pdaxrom/N64cart/pics/IMG_20220826_213916.jpg

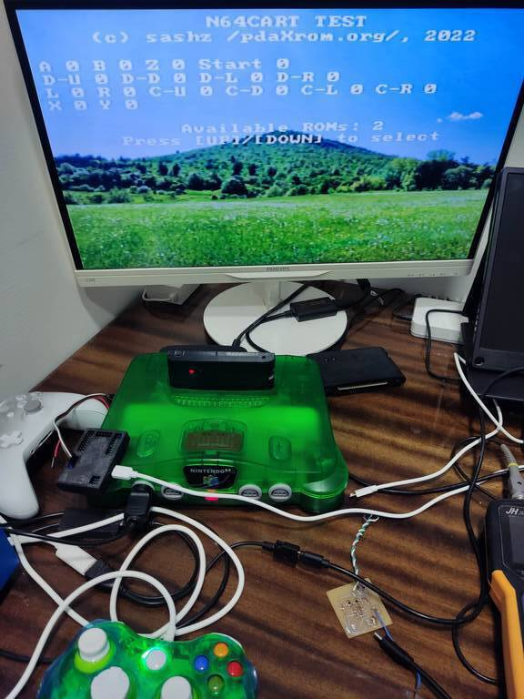
pics/IMG_20220826_213916.jpg
