pdaxrom/N64cart/rom/assets/UbuntuMono-Regular-8.png

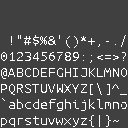
rom/assets/UbuntuMono-Regular-8.png
