pdaxrom/N64cart/fw/n64.h

/**
 * Copyright (c) 2022 Konrad Beckmann
 *
 * Copyright (c) 2022-2026 sashz /pdaXrom.org/
 *
 * SPDX-License-Identifier: BSD-3-Clause
 */

#pragma once

#define N64_AD0  0
#define N64_AD1  1
#define N64_AD2  2
#define N64_AD3  3
#define N64_AD4  4
#define N64_AD5  5
#define N64_AD6  6
#define N64_AD7  7
#define N64_AD8  8
#define N64_AD9  9
#define N64_AD10 10
#define N64_AD11 11
#define N64_AD12 12
#define N64_AD13 13
#define N64_AD14 14
#define N64_AD15 15
#define N64_ALEL 16
#define N64_ALEH 17
#define N64_WRITE 18
#define N64_READ 19
#define N64_CIC_DCLK    (20)
#define N64_CIC_DIO     (21)
#define N64_COLD_RESET  (22)

#ifdef N64CART_RP2040_PICO_LITE

#define N64_SI_DATA (25)
#define N64_SI_CLK (26)
#define N64_NMI (27)
#define N64_INT (28)

#else

#define N64_SI_DATA (23)
#define N64_SI_CLK (24)
#define N64_NMI (26)
#define N64_INT (27)

#endif
