pdaxrom/N64cart/fw/romfs/newlib-romfs.h

#ifndef __NEWLIB_ROMFS_H__
#define __NEWLIB_ROMFS_H__

#include <sys/types.h>

#ifdef __cplusplus
extern "C" {
#endif

int newlib_romfs_init(void);

#ifdef __cplusplus
}
#endif

#endif /* __NEWLIB_ROMFS_H__ */
