pdaxrom/N64cart/fw/romfs/test.c

/**
 * Copyright (c) 2022-2023 sashz /pdaXrom.org/
 *
 * SPDX-License-Identifier: BSD-3-Clause
 */

#include <stdio.h>
#include <stdlib.h>
#include <string.h>
#include <stdbool.h>
#include <errno.h>
#include <inttypes.h>
#include "romfs.h"
#include "test_flash.h"

#if defined(__linux__) || defined(__APPLE__)
#define ANSI_COLOR_RED     "\x1b[31m"
#define ANSI_COLOR_GREEN   "\x1b[32m"
#define ANSI_COLOR_YELLOW  "\x1b[33m"
#define ANSI_COLOR_CYAN    "\x1b[36m"
#define ANSI_COLOR_MAGENTA "\x1b[35m"
#define ANSI_COLOR_RESET   "\x1b[0m"
#else
#define ANSI_COLOR_RED     ""
#define ANSI_COLOR_GREEN   ""
#define ANSI_COLOR_YELLOW  ""
#define ANSI_COLOR_CYAN    ""
#define ANSI_COLOR_MAGENTA ""
#define ANSI_COLOR_RESET   ""
#endif

static uint8_t *flash_base = NULL;

const int NORMAL_CHUNK_SIZE = 256;
const int NORMAL_CHUNKS_PER_FILE = 20; // Creates 5KB files (256 * 20)
const int SMALL_FILE_SIZE = 1; // For testing file list limits

typedef struct {
    char name[ROMFS_MAX_NAME_LEN];
    uint32_t size;
    int file_index;
} random_fill_entry;

static uint32_t rng_state;
static uint64_t rng_calls;

/* Explicit 32-bit arithmetic gives the same sequence on every host libc. */
static uint32_t test_random(void)
{
    rng_state = rng_state * 1664525u + 1013904223u;
    rng_calls++;
    return rng_state;
}

static void free_file_list(char **files, int count)
{
    for (int i = 0; i < count; i++) {
        free(files[i]);
    }
    free(files);
}

static bool flash_ok(void)
{
    const test_flash_stats *stats = test_flash_get_stats();
    return stats->rejected == 0 && stats->injected == 0;
}

static bool close_test_file(romfs_file *file)
{
    uint32_t err = romfs_close_file(file);
    if (err != ROMFS_NOERR) {
        fprintf(stderr, "Failed to close %s: %s\n", file->entry.name, romfs_strerror(err));
        return false;
    }
    return true;
}

// Fills a buffer with deterministic dummy data based on an index
static void create_test_data(uint8_t *buffer, size_t size, int file_idx, int chunk_idx)
{
    for (size_t i = 0; i < size; i++) {
        buffer[i] = (uint8_t)((file_idx + chunk_idx + i) & 0xFF);
    }
}

static bool test_service_sector_protection(uint16_t *flash_map, uint32_t map_size)
{
    printf(ANSI_COLOR_YELLOW "\n--- Running Service Sector Protection Test ---\n" ANSI_COLOR_RESET);

    if (!romfs_format()) {
        fprintf(stderr, ANSI_COLOR_RED "Failed to format filesystem for service sector test\n" ANSI_COLOR_RESET);
        return false;
    }

    romfs_entry firmware = {0};
    romfs_entry flashmap = {0};
    if (romfs_get_entry("firmware", &firmware) != ROMFS_NOERR ||
            romfs_get_entry("flashmap", &flashmap) != ROMFS_NOERR) {
        fprintf(stderr, ANSI_COLOR_RED "Cannot read service entries\n" ANSI_COLOR_RESET);
        return false;
    }

    uint32_t first_data_sector = flashmap.start +
                                 (flashmap.size + ROMFS_FLASH_SECTOR - 1) / ROMFS_FLASH_SECTOR;
    uint32_t total_sectors = map_size / sizeof(uint16_t);
    if (first_data_sector >= total_sectors || firmware.size > first_data_sector * ROMFS_FLASH_SECTOR) {
        fprintf(stderr, ANSI_COLOR_RED "Invalid service sector layout\n" ANSI_COLOR_RESET);
        return false;
    }

    for (uint32_t i = 0; i < firmware.size; i++) {
        flash_base[i] = (uint8_t) ((i * 31u + 0x5au) & 0xffu);
    }

    // Simulate an old or damaged flash map that marks firmware and metadata
    // sectors as free. A user file must never be allocated in this range.
    for (uint32_t i = 0; i < first_data_sector; i++) {
        flash_map[i] = 0xffff;
    }

    uint8_t *io_buffer = malloc(ROMFS_FLASH_SECTOR);
    uint8_t *payload = malloc(ROMFS_FLASH_SECTOR);
    if (!io_buffer || !payload) {
        fprintf(stderr, ANSI_COLOR_RED "Allocation failure in service sector test\n" ANSI_COLOR_RESET);
        free(io_buffer);
        free(payload);
        return false;
    }
    memset(payload, 0xa5, ROMFS_FLASH_SECTOR);

    bool success = true;
    romfs_file file = {0};
    if (romfs_create_file("service-guard.bin", &file, ROMFS_MODE_READWRITE, ROMFS_TYPE_MISC,
                          io_buffer) != ROMFS_NOERR ||
            romfs_write_file(payload, ROMFS_FLASH_SECTOR, &file) != ROMFS_FLASH_SECTOR ||
            romfs_close_file(&file) != ROMFS_NOERR) {
        fprintf(stderr, ANSI_COLOR_RED "Failed to write service sector test file: %s\n" ANSI_COLOR_RESET,
                romfs_strerror(file.err));
        success = false;
        goto cleanup;
    }

    if (file.entry.start < first_data_sector) {
        fprintf(stderr, ANSI_COLOR_RED "User file allocated protected sector %u (< %u)\n" ANSI_COLOR_RESET,
                file.entry.start, first_data_sector);
        success = false;
        goto cleanup;
    }

    for (uint32_t i = 0; i < firmware.size; i++) {
        uint8_t expected = (uint8_t) ((i * 31u + 0x5au) & 0xffu);
        if (flash_base[i] != expected) {
            fprintf(stderr, ANSI_COLOR_RED "Firmware changed at offset 0x%08x\n" ANSI_COLOR_RESET, i);
            success = false;
            goto cleanup;
        }
    }

    romfs_file protected_file = {0};
    if (romfs_open_append("firmware", &protected_file, ROMFS_TYPE_MISC, io_buffer) != ROMFS_ERR_OPERATION ||
            romfs_delete("firmware") != ROMFS_ERR_OPERATION ||
            romfs_rename("firmware", "firmware.old") != ROMFS_ERR_OPERATION ||
            romfs_create_file("fake-service", &protected_file, ROMFS_MODE_READWRITE, ROMFS_TYPE_FIRMWARE,
                              io_buffer) != ROMFS_ERR_OPERATION) {
        fprintf(stderr, ANSI_COLOR_RED "Service entry mutation was not rejected\n" ANSI_COLOR_RESET);
        success = false;
    }

cleanup:
    romfs_delete("service-guard.bin");
    free(io_buffer);
    free(payload);
    success = romfs_format() && success;
    return success;
}

// Shuffles an array of strings
static void shuffle_filenames(char **array, size_t n)
{
    if (n > 1) {
        for (size_t i = 0; i < n - 1; i++) {
            size_t j = i + test_random() % (n - i);
            char *t = array[j];
            array[j] = array[i];
            array[i] = t;
        }
    }
}

// Gets a list of all user-created files
static int get_file_list(char ***file_list_out)
{
    *file_list_out = NULL;
    int count = 0;
    int capacity = 128;
    char **files = malloc(capacity * sizeof(*files));
    if (!files) {
        fprintf(stderr, "Failed to allocate file list\n");
        return -1;
    }

    romfs_file file = {0};
    uint32_t err = romfs_list(&file, true);
    while (err == ROMFS_NOERR) {
        if (file.entry.attr.names.type == ROMFS_TYPE_MISC) {
            if (count == capacity) {
                int new_capacity = capacity * 2;
                char **new_files = realloc(files, new_capacity * sizeof(*files));
                if (!new_files) {
                    fprintf(stderr, "Failed to expand file list\n");
                    free_file_list(files, count);
                    return -1;
                }
                files = new_files;
                capacity = new_capacity;
            }
            files[count] = strdup(file.entry.name);
            if (!files[count]) {
                fprintf(stderr, "Failed to copy filename\n");
                free_file_list(files, count);
                return -1;
            }
            count++;
        }
        err = romfs_list(&file, false);
    }
    if (err != ROMFS_ERR_NO_FREE_ENTRIES) {
        fprintf(stderr, "Failed to list files: %s\n", romfs_strerror(err));
        free_file_list(files, count);
        return -1;
    }
    *file_list_out = files;
    return count;
}

// Returns the number of complete files, or -1 on an unexpected failure.
// NO_SPACE / NO_FREE_ENTRIES are expected only in these capacity scenarios.
static int fill_drive(const char *prefix, int max_chunks_per_file, int chunk_size, bool random_size)
{
    int file_idx = 0;
    int result = -1;
    uint8_t *test_data = malloc(chunk_size);
    uint8_t *io_buffer = malloc(ROMFS_FLASH_SECTOR);
    if (!test_data || !io_buffer) {
        fprintf(stderr, "Failed to allocate fill buffers\n");
        goto cleanup;
    }

    while (true) {
        char filename[ROMFS_MAX_NAME_LEN];
        snprintf(filename, sizeof(filename), "%s%04d.dat", prefix, file_idx);
        romfs_file file = {0};
        uint32_t err = romfs_create_file(filename, &file, ROMFS_MODE_READWRITE, ROMFS_TYPE_MISC, io_buffer);
        if (err != ROMFS_NOERR) {
            if (err == ROMFS_ERR_NO_FREE_ENTRIES || err == ROMFS_ERR_NO_SPACE) {
                printf("\nCapacity reached after %d files: %s\n", file_idx, romfs_strerror(err));
                result = file_idx;
            } else {
                fprintf(stderr, "Failed to create %s: %s\n", filename, romfs_strerror(err));
            }
            break;
        }

        printf(ANSI_COLOR_MAGENTA "Creating %s... \r" ANSI_COLOR_RESET, filename);
        fflush(stdout);
        int chunks = random_size ? 1 + test_random() % max_chunks_per_file : max_chunks_per_file;
        bool no_space = false;
        bool write_ok = true;
        for (int j = 0; j < chunks; j++) {
            create_test_data(test_data, chunk_size, file_idx, j);
            uint32_t written = romfs_write_file(test_data, chunk_size, &file);
            if (written != (uint32_t)chunk_size || file.err != ROMFS_NOERR) {
                no_space = file.err == ROMFS_ERR_NO_SPACE && written < (uint32_t)chunk_size;
                write_ok = false;
                if (!no_space) {
                    fprintf(stderr, "Write failed for %s: %u/%d bytes, %s\n",
                            filename, written, chunk_size, romfs_strerror(file.err));
                }
                break;
            }
        }
        uint32_t close_err = romfs_close_file(&file);
        if (close_err != ROMFS_NOERR) {
            fprintf(stderr, "Close failed for %s: %s\n", filename, romfs_strerror(close_err));
            break;
        }
        if (!write_ok) {
            if (!no_space) {
                break;
            }
            /* This set verifies complete files; test_io checks partial data. */
            err = romfs_delete(filename);
            if (err != ROMFS_NOERR) {
                fprintf(stderr, "Failed to discard %s: %s\n", filename, romfs_strerror(err));
                break;
            }
            printf("\nData space exhausted after %d complete files.\n", file_idx);
            result = file_idx;
            break;
        }
        file_idx++;
    }

cleanup:
    free(io_buffer);
    free(test_data);
    return result;
}

// Verifies the contents of all user files on the drive, works with random sizes.
static bool verify_drive(uint32_t chunk_size)
{
    printf(ANSI_COLOR_CYAN "\nVerifying all files...\n" ANSI_COLOR_RESET);
    bool success = true;
    char** file_list = NULL;
    int file_count = get_file_list(&file_list);
    if (file_count <= 0) {
        if (file_list) {
            free(file_list);
        }
        if (file_count == 0) {
            printf("No files to verify.\n");
            return true;
        }
        return false;
    }

    uint8_t* read_buffer = malloc(chunk_size);
    uint8_t* expected_data = malloc(chunk_size);
    if (!read_buffer || !expected_data) {
        free(read_buffer);
        free(expected_data);
        free_file_list(file_list, file_count);
        fprintf(stderr, "Failed to allocate verification buffers\n");
        return false;
    }

    for (int i = 0; i < file_count; i++) {
        printf(ANSI_COLOR_MAGENTA "Verifying %s... \r" ANSI_COLOR_RESET, file_list[i]);
        fflush(stdout);

        int file_idx = -1;
        if (sscanf(file_list[i], "file%d.dat", &file_idx) != 1) {
            if (sscanf(file_list[i], "rfile%d.dat", &file_idx) != 1) {
                if (sscanf(file_list[i], "ifile%d.dat", &file_idx) != 1) {
                    if (sscanf(file_list[i], "rndfile%d.dat", &file_idx) != 1) {
                        sscanf(file_list[i], "sfile%d.dat", &file_idx);
                    }
                }
            }
        }

        if (file_idx < 0) {
            fprintf(stderr, "Unexpected verification filename: %s\n", file_list[i]);
            success = false;
            continue;
        }
        romfs_file file = {0};
        uint8_t *romfs_io_buffer = malloc(ROMFS_FLASH_SECTOR);
        if (!romfs_io_buffer) {
            fprintf(stderr, "Failed to allocate verification IO buffer\n");
            success = false;
            break;
        }
        if (romfs_open_file(file_list[i], &file, romfs_io_buffer) != ROMFS_NOERR) {
            fprintf(stderr, ANSI_COLOR_RED "\nFailed to open file for verification: %s\n" ANSI_COLOR_RESET, file_list[i]);
            success = false;
            free(romfs_io_buffer);
            continue;
        }

        bool file_ok = true;
        uint32_t total_bytes_read = 0;
        int chunk_idx = 0;
        while(total_bytes_read < file.entry.size) {
            uint32_t remaining_bytes = file.entry.size - total_bytes_read;
            uint32_t bytes_to_read = remaining_bytes > chunk_size ? chunk_size : remaining_bytes;

            uint32_t bytes_read = romfs_read_file(read_buffer, bytes_to_read, &file);
            if (bytes_read != bytes_to_read ||
                    (file.err != ROMFS_NOERR && file.err != ROMFS_ERR_EOF)) {
                fprintf(stderr, ANSI_COLOR_RED "\nRead error on %s, chunk %d. Expected %d, got %d\n" ANSI_COLOR_RESET, file_list[i],
                        chunk_idx, bytes_to_read, bytes_read);
                file_ok = false;
                break;
            }

            create_test_data(expected_data, bytes_to_read, file_idx, chunk_idx);
            if (memcmp(read_buffer, expected_data, bytes_to_read) != 0) {
                fprintf(stderr, ANSI_COLOR_RED "\nData mismatch in %s, chunk %d\n" ANSI_COLOR_RESET, file_list[i], chunk_idx);
                file_ok = false;
                break;
            }
            total_bytes_read += bytes_read;
            chunk_idx++;
        }

        if (romfs_close_file(&file) != ROMFS_NOERR) {
            fprintf(stderr, "Close failed for %s\n", file_list[i]);
            file_ok = false;
        }
        free(romfs_io_buffer);
        if (!file_ok) {
            success = false;
        }
    }

    for(int i=0; i<file_count; i++) {
        free(file_list[i]);
    }
    free(file_list);
    free(read_buffer);
    free(expected_data);

    if(success) {
        printf(ANSI_COLOR_GREEN "\nVerification successful. All %d files are correct.\n" ANSI_COLOR_RESET, file_count);
    } else {
        printf(ANSI_COLOR_RED "\nVerification FAILED.\n" ANSI_COLOR_RESET);
    }

    return success;
}

static bool test_large_io_transfer(void)
{
    printf(ANSI_COLOR_YELLOW "\n--- Running Large I/O Transfer Test (> ROMFS_FLASH_SECTOR) ---\n" ANSI_COLOR_RESET);

    if (!romfs_format()) {
        fprintf(stderr, ANSI_COLOR_RED "Failed to format filesystem for large I/O test\n" ANSI_COLOR_RESET);
        return false;
    }

    const uint32_t large_len = (ROMFS_FLASH_SECTOR * 2) + 123;
    uint8_t *write_data = malloc(large_len);
    uint8_t *read_data = malloc(large_len);
    uint8_t *io_buffer = malloc(ROMFS_FLASH_SECTOR);
    bool success = false;

    if (!write_data || !read_data || !io_buffer) {
        fprintf(stderr, ANSI_COLOR_RED "Allocation failure in large I/O test\n" ANSI_COLOR_RESET);
        goto cleanup;
    }

    for (uint32_t i = 0; i < large_len; i++) {
        write_data[i] = (uint8_t)(i ^ 0x5a);
    }

    romfs_file file;
    if (romfs_create_file("large_test.bin", &file, ROMFS_MODE_READWRITE, ROMFS_TYPE_MISC, io_buffer) != ROMFS_NOERR) {
        fprintf(stderr, ANSI_COLOR_RED "Failed to create large_test.bin: %s\n" ANSI_COLOR_RESET, romfs_strerror(file.err));
        goto cleanup;
    }

    uint32_t written = romfs_write_file(write_data, large_len, &file);
    if (written != large_len || file.err != ROMFS_NOERR) {
        fprintf(stderr, ANSI_COLOR_RED "Write failed for large_test.bin (wrote %u/%u): %s\n" ANSI_COLOR_RESET,
                written, large_len, romfs_strerror(file.err));
        goto cleanup_close_write;
    }

    if (romfs_close_file(&file) != ROMFS_NOERR) {
        fprintf(stderr, ANSI_COLOR_RED "Close failed for large_test.bin after write: %s\n" ANSI_COLOR_RESET,
                romfs_strerror(file.err));
        goto cleanup_close_write;
    }

    romfs_file reader;
    if (romfs_open_file("large_test.bin", &reader, io_buffer) != ROMFS_NOERR) {
        fprintf(stderr, ANSI_COLOR_RED "Failed to reopen large_test.bin: %s\n" ANSI_COLOR_RESET, romfs_strerror(reader.err));
        goto cleanup_close_write;
    }

    uint32_t read_total = romfs_read_file(read_data, large_len, &reader);
    if (read_total != large_len) {
        fprintf(stderr, ANSI_COLOR_RED "Read failed for large_test.bin (read %u/%u): %s\n" ANSI_COLOR_RESET,
                read_total, large_len, romfs_strerror(reader.err));
        success = close_test_file(&reader) && success;
        goto cleanup_close_write;
    }

    if (reader.err != ROMFS_ERR_EOF) {
        fprintf(stderr, ANSI_COLOR_RED "Unexpected reader.err (%u) after large read\n" ANSI_COLOR_RESET, reader.err);
        success = close_test_file(&reader) && success;
        goto cleanup_close_write;
    }

    if (memcmp(write_data, read_data, large_len) != 0) {
        fprintf(stderr, ANSI_COLOR_RED "Data mismatch after large I/O transfer\n" ANSI_COLOR_RESET);
        success = close_test_file(&reader) && success;
        goto cleanup_close_write;
    }

    if (romfs_close_file(&reader) != ROMFS_NOERR) {
        fprintf(stderr, ANSI_COLOR_RED "Close failed for reader handle: %s\n" ANSI_COLOR_RESET, romfs_strerror(reader.err));
        goto cleanup_close_write;
    }

    success = true;

cleanup_close_write:
    romfs_delete("large_test.bin");

cleanup:
    free(write_data);
    free(read_data);
    free(io_buffer);
    success = romfs_format() && success;
    return success;
}

static bool test_seek_tell(void)
{
    printf(ANSI_COLOR_YELLOW "\n--- Running Seek/Tell Test ---\n" ANSI_COLOR_RESET);

    if (!romfs_format()) {
        fprintf(stderr, ANSI_COLOR_RED "Failed to format filesystem for seek/tell test\n" ANSI_COLOR_RESET);
        return false;
    }

    const uint32_t total_len = ROMFS_FLASH_SECTOR * 3 + 321;
    const size_t read_buf_size = 512;

    uint8_t *pattern = malloc(total_len);
    uint8_t *write_io = malloc(ROMFS_FLASH_SECTOR);
    uint8_t *read_io = malloc(ROMFS_FLASH_SECTOR);
    uint8_t *read_buf = malloc(read_buf_size);
    bool success = true;

    if (!pattern || !write_io || !read_io || !read_buf) {
        fprintf(stderr, ANSI_COLOR_RED "Allocation failure in seek/tell test\n" ANSI_COLOR_RESET);
        success = false;
        goto cleanup;
    }

    for (uint32_t i = 0; i < total_len; i++) {
        pattern[i] = (uint8_t)(i & 0xff);
    }

    romfs_file file;
    if (romfs_create_file("seektest.bin", &file, ROMFS_MODE_READWRITE, ROMFS_TYPE_MISC, write_io) != ROMFS_NOERR) {
        fprintf(stderr, ANSI_COLOR_RED "Failed to create seektest.bin: %s\n" ANSI_COLOR_RESET, romfs_strerror(file.err));
        success = false;
        goto cleanup;
    }

    if (romfs_write_file(pattern, total_len, &file) != total_len || romfs_close_file(&file) != ROMFS_NOERR) {
        fprintf(stderr, ANSI_COLOR_RED "Failed to populate seektest.bin: %s\n" ANSI_COLOR_RESET, romfs_strerror(file.err));
        success = false;
        goto cleanup;
    }

    romfs_file reader;
    if (romfs_open_file("seektest.bin", &reader, read_io) != ROMFS_NOERR) {
        fprintf(stderr, ANSI_COLOR_RED "Failed to open seektest.bin for reading: %s\n" ANSI_COLOR_RESET,
                romfs_strerror(reader.err));
        success = false;
        goto cleanup;
    }

    uint32_t pos = 0;
    if (romfs_tell_file(&reader, &pos) != ROMFS_NOERR || pos != 0) {
        fprintf(stderr, ANSI_COLOR_RED "Initial tell mismatch (%u)\n" ANSI_COLOR_RESET, pos);
        success = false;
        goto cleanup_reader;
    }

    const uint32_t first_seek = ROMFS_FLASH_SECTOR + 123;
    if (romfs_seek_file(&reader, (int32_t)first_seek, SEEK_SET) != ROMFS_NOERR) {
        fprintf(stderr, ANSI_COLOR_RED "SEEK_SET to %u failed: %s\n" ANSI_COLOR_RESET, first_seek, romfs_strerror(reader.err));
        success = false;
        goto cleanup_reader;
    }
    if (romfs_tell_file(&reader, &pos) != ROMFS_NOERR || pos != first_seek) {
        fprintf(stderr, ANSI_COLOR_RED "Tell after SEEK_SET mismatch (%u)\n" ANSI_COLOR_RESET, pos);
        success = false;
        goto cleanup_reader;
    }

    const uint32_t first_read = 200;
    if (romfs_read_file(read_buf, first_read, &reader) != first_read ||
            memcmp(read_buf, &pattern[first_seek], first_read) != 0) {
        fprintf(stderr, ANSI_COLOR_RED "Data mismatch after SEEK_SET read\n" ANSI_COLOR_RESET);
        success = false;
        goto cleanup_reader;
    }

    uint32_t expected_pos = first_seek + first_read;
    if (romfs_tell_file(&reader, &pos) != ROMFS_NOERR || pos != expected_pos) {
        fprintf(stderr, ANSI_COLOR_RED "Tell after first read mismatch (%u)\n" ANSI_COLOR_RESET, pos);
        success = false;
        goto cleanup_reader;
    }

    if (romfs_seek_file(&reader, -50, SEEK_CUR) != ROMFS_NOERR) {
        fprintf(stderr, ANSI_COLOR_RED "SEEK_CUR -50 failed: %s\n" ANSI_COLOR_RESET, romfs_strerror(reader.err));
        success = false;
        goto cleanup_reader;
    }
    expected_pos -= 50;
    if (romfs_tell_file(&reader, &pos) != ROMFS_NOERR || pos != expected_pos) {
        fprintf(stderr, ANSI_COLOR_RED "Tell after SEEK_CUR mismatch (%u)\n" ANSI_COLOR_RESET, pos);
        success = false;
        goto cleanup_reader;
    }

    const uint32_t second_read = 100;
    if (romfs_read_file(read_buf, second_read, &reader) != second_read ||
            memcmp(read_buf, &pattern[expected_pos], second_read) != 0) {
        fprintf(stderr, ANSI_COLOR_RED "Data mismatch after SEEK_CUR read\n" ANSI_COLOR_RESET);
        success = false;
        goto cleanup_reader;
    }
    expected_pos += second_read;

    if (romfs_seek_file(&reader, -128, SEEK_END) != ROMFS_NOERR) {
        fprintf(stderr, ANSI_COLOR_RED "SEEK_END -128 failed: %s\n" ANSI_COLOR_RESET, romfs_strerror(reader.err));
        success = false;
        goto cleanup_reader;
    }
    expected_pos = total_len - 128;
    if (romfs_tell_file(&reader, &pos) != ROMFS_NOERR || pos != expected_pos) {
        fprintf(stderr, ANSI_COLOR_RED "Tell after SEEK_END mismatch (%u)\n" ANSI_COLOR_RESET, pos);
        success = false;
        goto cleanup_reader;
    }

    const uint32_t third_read = 64;
    if (romfs_read_file(read_buf, third_read, &reader) != third_read ||
            memcmp(read_buf, &pattern[expected_pos], third_read) != 0) {
        fprintf(stderr, ANSI_COLOR_RED "Data mismatch after SEEK_END read\n" ANSI_COLOR_RESET);
        success = false;
        goto cleanup_reader;
    }
    expected_pos += third_read;

    if (romfs_seek_file(&reader, 0, SEEK_END) != ROMFS_NOERR) {
        fprintf(stderr, ANSI_COLOR_RED "SEEK_END 0 failed: %s\n" ANSI_COLOR_RESET, romfs_strerror(reader.err));
        success = false;
        goto cleanup_reader;
    }
    if (romfs_read_file(read_buf, 16, &reader) != 0 || reader.err != ROMFS_ERR_EOF) {
        fprintf(stderr, ANSI_COLOR_RED "EOF read after SEEK_END did not behave as expected\n" ANSI_COLOR_RESET);
        success = false;
        goto cleanup_reader;
    }

cleanup_reader:
    success = close_test_file(&reader) && success;

    if (success) {
        romfs_file empty_file;
        if (romfs_create_file("empty_seek.bin", &file, ROMFS_MODE_READWRITE, ROMFS_TYPE_MISC, write_io) != ROMFS_NOERR) {
            fprintf(stderr, ANSI_COLOR_RED "Failed to create empty_seek.bin: %s\n" ANSI_COLOR_RESET, romfs_strerror(file.err));
            success = false;
        } else if (romfs_close_file(&file) != ROMFS_NOERR) {
            fprintf(stderr, ANSI_COLOR_RED "Failed to close empty_seek.bin after creation: %s\n" ANSI_COLOR_RESET,
                    romfs_strerror(file.err));
            success = false;
        } else if (romfs_open_file("empty_seek.bin", &empty_file, read_io) != ROMFS_NOERR) {
            fprintf(stderr, ANSI_COLOR_RED "Failed to open empty_seek.bin: %s\n" ANSI_COLOR_RESET, romfs_strerror(empty_file.err));
            success = false;
        } else {
            if (romfs_tell_file(&empty_file, &pos) != ROMFS_NOERR || pos != 0) {
                fprintf(stderr, ANSI_COLOR_RED "Empty file tell mismatch\n" ANSI_COLOR_RESET);
                success = false;
            }
            if (success && romfs_seek_file(&empty_file, 0, SEEK_SET) != ROMFS_NOERR) {
                fprintf(stderr, ANSI_COLOR_RED "Empty file SEEK_SET failed\n" ANSI_COLOR_RESET);
                success = false;
            }
            if (success && romfs_seek_file(&empty_file, 0, SEEK_END) != ROMFS_NOERR) {
                fprintf(stderr, ANSI_COLOR_RED "Empty file SEEK_END failed\n" ANSI_COLOR_RESET);
                success = false;
            }
            if (success && romfs_seek_file(&empty_file, 1, SEEK_SET) == ROMFS_NOERR) {
                fprintf(stderr, ANSI_COLOR_RED "Empty file SEEK_SET beyond end unexpectedly succeeded\n" ANSI_COLOR_RESET);
                success = false;
            }
            if (success && romfs_seek_file(&empty_file, -1, SEEK_CUR) == ROMFS_NOERR) {
                fprintf(stderr, ANSI_COLOR_RED "Empty file SEEK_CUR negative unexpectedly succeeded\n" ANSI_COLOR_RESET);
                success = false;
            }
            success = close_test_file(&empty_file) && success;
        }
    }

cleanup:
    success = romfs_format() && success;
    free(pattern);
    free(write_io);
    free(read_io);
    free(read_buf);
    return success;
}

static bool test_append_mode(void)
{
    printf(ANSI_COLOR_YELLOW "\n--- Running Append Mode Test ---\n" ANSI_COLOR_RESET);

    if (!romfs_format()) {
        fprintf(stderr, ANSI_COLOR_RED "Failed to format filesystem for append test\n" ANSI_COLOR_RESET);
        return false;
    }

    const char part1[] = "append-one-";
    const char part2[] = "append-two-extended";
    const size_t part1_len = strlen(part1);
    const size_t part2_len = strlen(part2);
    const size_t big_len = ROMFS_FLASH_SECTOR + 137;
    const size_t total_expected = part1_len + part2_len + big_len;

    uint8_t *io_buffer = malloc(ROMFS_FLASH_SECTOR);
    uint8_t *read_io_buffer = malloc(ROMFS_FLASH_SECTOR);
    uint8_t *big_data = malloc(big_len);
    uint8_t *read_buffer = malloc(total_expected);
    uint8_t *expected = malloc(total_expected);

    if (!io_buffer || !read_io_buffer || !big_data || !read_buffer || !expected) {
        fprintf(stderr, ANSI_COLOR_RED "Allocation failure in append test\n" ANSI_COLOR_RESET);
        free(io_buffer);
        free(read_io_buffer);
        free(big_data);
        free(read_buffer);
        free(expected);
        return false;
    }

    create_test_data(big_data, big_len, 77, 0);

    bool success = true;
    uint32_t pos = 0;
    romfs_file file = {0};
    romfs_file reader = {0};

    /* Step 1: create via append and write first chunk */
    if (romfs_open_append_path("append.bin", &file, ROMFS_TYPE_MISC, io_buffer, false) != ROMFS_NOERR) {
        fprintf(stderr, ANSI_COLOR_RED "Failed to open append.bin for append: %s\n" ANSI_COLOR_RESET, romfs_strerror(file.err));
        success = false;
        goto cleanup;
    }

    if (romfs_write_file(part1, part1_len, &file) != part1_len) {
        fprintf(stderr, ANSI_COLOR_RED "Failed to write first append chunk\n" ANSI_COLOR_RESET);
        success = false;
        goto cleanup_close_file;
    }

    if (romfs_tell_file(&file, &pos) != ROMFS_NOERR || pos != part1_len) {
        fprintf(stderr, ANSI_COLOR_RED "tell mismatch after initial append (got %u, expected %zu)\n" ANSI_COLOR_RESET, pos,
                part1_len);
        success = false;
        goto cleanup_close_file;
    }

cleanup_close_file:
    if (romfs_close_file(&file) != ROMFS_NOERR) {
        fprintf(stderr, ANSI_COLOR_RED "Failed to close append.bin after first write: %s\n" ANSI_COLOR_RESET,
                romfs_strerror(file.err));
        success = false;
    }
    if (!success) {
        goto cleanup;
    }

    /* Verify initial contents */
    memset(&reader, 0, sizeof(reader));
    if (romfs_open_file("append.bin", &reader, read_io_buffer) != ROMFS_NOERR) {
        fprintf(stderr, ANSI_COLOR_RED "Failed to reopen append.bin for verification: %s\n" ANSI_COLOR_RESET,
                romfs_strerror(reader.err));
        success = false;
        goto cleanup;
    }
    if (romfs_read_file(read_buffer, part1_len, &reader) != part1_len ||
            memcmp(read_buffer, part1, part1_len) != 0) {
        fprintf(stderr, ANSI_COLOR_RED "Initial append verification failed\n" ANSI_COLOR_RESET);
        success = false;
    }
    success = close_test_file(&reader) && success;
    if (!success) {
        goto cleanup;
    }

    /* Step 2: append second chunk within same sector */
    memset(&file, 0, sizeof(file));
    if (romfs_open_append_path("append.bin", &file, ROMFS_TYPE_MISC, io_buffer, false) != ROMFS_NOERR) {
        fprintf(stderr, ANSI_COLOR_RED "Failed to reopen append.bin for second append: %s\n" ANSI_COLOR_RESET,
                romfs_strerror(file.err));
        success = false;
        goto cleanup;
    }

    if (romfs_tell_file(&file, &pos) != ROMFS_NOERR || pos != part1_len) {
        fprintf(stderr, ANSI_COLOR_RED "tell mismatch before second append (got %u)\n" ANSI_COLOR_RESET, pos);
        success = false;
        goto cleanup_second_close;
    }

    if (romfs_write_file(part2, part2_len, &file) != part2_len) {
        fprintf(stderr, ANSI_COLOR_RED "Failed to write second append chunk\n" ANSI_COLOR_RESET);
        success = false;
        goto cleanup_second_close;
    }

    if (romfs_tell_file(&file, &pos) != ROMFS_NOERR || pos != part1_len + part2_len) {
        fprintf(stderr, ANSI_COLOR_RED "tell mismatch after second append (got %u, expected %zu)\n" ANSI_COLOR_RESET, pos,
                part1_len + part2_len);
        success = false;
        goto cleanup_second_close;
    }

cleanup_second_close:
    if (romfs_close_file(&file) != ROMFS_NOERR) {
        fprintf(stderr, ANSI_COLOR_RED "Failed to close append.bin after second write: %s\n" ANSI_COLOR_RESET,
                romfs_strerror(file.err));
        success = false;
    }
    if (!success) {
        goto cleanup;
    }

    /* Verify combined content */
    memcpy(expected, part1, part1_len);
    memcpy(expected + part1_len, part2, part2_len);
    memset(&reader, 0, sizeof(reader));
    if (romfs_open_file("append.bin", &reader, read_io_buffer) != ROMFS_NOERR) {
        fprintf(stderr, ANSI_COLOR_RED "Failed to reopen append.bin for second verification: %s\n" ANSI_COLOR_RESET,
                romfs_strerror(reader.err));
        success = false;
        goto cleanup;
    }
    size_t current_size = part1_len + part2_len;
    if (romfs_read_file(read_buffer, current_size, &reader) != current_size ||
            memcmp(read_buffer, expected, current_size) != 0) {
        fprintf(stderr, ANSI_COLOR_RED "Second append verification failed\n" ANSI_COLOR_RESET);
        success = false;
    }
    success = close_test_file(&reader) && success;
    if (!success) {
        goto cleanup;
    }

    /* Step 3: append data crossing sector boundary */
    memset(&file, 0, sizeof(file));
    if (romfs_open_append_path("append.bin", &file, ROMFS_TYPE_MISC, io_buffer, false) != ROMFS_NOERR) {
        fprintf(stderr, ANSI_COLOR_RED "Failed to reopen append.bin for large append: %s\n" ANSI_COLOR_RESET,
                romfs_strerror(file.err));
        success = false;
        goto cleanup;
    }

    if (romfs_tell_file(&file, &pos) != ROMFS_NOERR || pos != current_size) {
        fprintf(stderr, ANSI_COLOR_RED "tell mismatch before large append (got %u, expected %zu)\n" ANSI_COLOR_RESET, pos,
                current_size);
        success = false;
        goto cleanup_large_close;
    }

    if (romfs_write_file(big_data, big_len, &file) != big_len) {
        fprintf(stderr, ANSI_COLOR_RED "Failed to write large append payload\n" ANSI_COLOR_RESET);
        success = false;
        goto cleanup_large_close;
    }

    if (romfs_tell_file(&file, &pos) != ROMFS_NOERR || pos != current_size + big_len) {
        fprintf(stderr, ANSI_COLOR_RED "tell mismatch after large append (got %u, expected %zu)\n" ANSI_COLOR_RESET, pos,
                current_size + big_len);
        success = false;
        goto cleanup_large_close;
    }

cleanup_large_close:
    if (romfs_close_file(&file) != ROMFS_NOERR) {
        fprintf(stderr, ANSI_COLOR_RED "Failed to close append.bin after large append: %s\n" ANSI_COLOR_RESET,
                romfs_strerror(file.err));
        success = false;
    }
    if (!success) {
        goto cleanup;
    }

    /* Verify final content */
    memcpy(expected + current_size, big_data, big_len);
    memset(&reader, 0, sizeof(reader));
    if (romfs_open_file("append.bin", &reader, read_io_buffer) != ROMFS_NOERR) {
        fprintf(stderr, ANSI_COLOR_RED "Failed to open append.bin for final verification: %s\n" ANSI_COLOR_RESET,
                romfs_strerror(reader.err));
        success = false;
        goto cleanup;
    }
    if (romfs_read_file(read_buffer, total_expected, &reader) != total_expected ||
            memcmp(read_buffer, expected, total_expected) != 0) {
        fprintf(stderr, ANSI_COLOR_RED "Final append verification failed\n" ANSI_COLOR_RESET);
        success = false;
    }
    success = close_test_file(&reader) && success;
    if (!success) {
        goto cleanup;
    }

    /* Flat namespace append helper */
    memset(&file, 0, sizeof(file));
    if (romfs_open_append("flat.bin", &file, ROMFS_TYPE_MISC, io_buffer) != ROMFS_NOERR) {
        fprintf(stderr, ANSI_COLOR_RED "Failed to open flat.bin via romfs_open_append: %s\n" ANSI_COLOR_RESET,
                romfs_strerror(file.err));
        success = false;
        goto cleanup;
    }
    if (romfs_write_file(part1, part1_len, &file) != part1_len || romfs_close_file(&file) != ROMFS_NOERR) {
        fprintf(stderr, ANSI_COLOR_RED "Failed to use romfs_open_append in flat mode\n" ANSI_COLOR_RESET);
        success = false;
        goto cleanup;
    }
    if (romfs_open_file("flat.bin", &reader, io_buffer) != ROMFS_NOERR) {
        fprintf(stderr, ANSI_COLOR_RED "Failed to reopen flat.bin after append\n" ANSI_COLOR_RESET);
        success = false;
        goto cleanup;
    }
    if (romfs_read_file(read_buffer, part1_len, &reader) != part1_len ||
            memcmp(read_buffer, part1, part1_len) != 0) {
        fprintf(stderr, ANSI_COLOR_RED "Verification of flat.bin append failed\n" ANSI_COLOR_RESET);
        success = false;
    }
    success = close_test_file(&reader) && success;
    if (!success) {
        goto cleanup;
    }

    /* Ensure create_dirs parameter works */
    memset(&file, 0, sizeof(file));
    if (romfs_open_append_path("logs/session/log.txt", &file, ROMFS_TYPE_MISC, io_buffer, true) != ROMFS_NOERR) {
        fprintf(stderr, ANSI_COLOR_RED "Failed to append with implicit directory creation: %s\n" ANSI_COLOR_RESET,
                romfs_strerror(file.err));
        success = false;
        goto cleanup;
    }
    if (romfs_close_file(&file) != ROMFS_NOERR) {
        fprintf(stderr, ANSI_COLOR_RED "Failed to close log.txt in append test: %s\n" ANSI_COLOR_RESET,
                romfs_strerror(file.err));
        success = false;
        goto cleanup;
    }
    romfs_delete_path("logs/session/log.txt");
    romfs_rmdir_path("logs/session");
    romfs_rmdir_path("logs");

cleanup:
    romfs_delete_path("append.bin");
    romfs_delete("flat.bin");
    success = romfs_format() && success;
    free(io_buffer);
    free(read_io_buffer);
    free(big_data);
    free(read_buffer);
    free(expected);
    return success;
}
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
