pdaxrom/N64cart/utils/romfs-gui/romfsdevice.cpp

#include "romfsdevice.h"

#include <QByteArray>
#include <QFile>
#include <QFileInfo>
#include <QSaveFile>
#include <QCoreApplication>
#include <QDebug>
#include <QDir>
#include <cstring>
#include <utility>

#include "romfs.h"

#include "remotetransport.h"
#include "romfsbridge.h"
#include "usbtransport.h"

namespace
{
static QByteArray toPathBytes(const QString &path)
{
    QString normalized = path;
    if (normalized.isEmpty()) {
        normalized = QStringLiteral("/");
    }
    if (normalized != QStringLiteral("/") && normalized.endsWith(QLatin1Char('/'))) {
        normalized.chop(1);
    }
    return normalized.toUtf8();
}

static QString buildChildPath(const QString &parent, const QString &name)
{
    if (parent.isEmpty() || parent == QLatin1String("/")) {
        return QStringLiteral("/%1").arg(name);
    }
    if (parent.endsWith(QLatin1Char('/'))) {
        return parent + name;
    }
    return parent + QLatin1Char('/') + name;
}

static QString combineErrors(const QString &primary, const QString &secondary)
{
    if (primary.isEmpty()) {
        return secondary;
    }
    if (secondary.isEmpty()) {
        return primary;
    }
    return QStringLiteral("%1 Cleanup failed: %2").arg(primary, secondary);
}
}

RomfsDevice::RomfsDevice(QObject *parent)
    : QObject(parent)
{
    flashBuffer_.resize(ROMFS_FLASH_SECTOR);
}

RomfsDevice::~RomfsDevice()
{
    disconnect();
}

bool RomfsDevice::connectUsb()
{
    disconnect();
    auto transport = std::make_unique<UsbTransport>(this);
    QString error;
    if (!transport->connectDevice(&error)) {
        setError(error);
        return false;
    }

    transport_ = std::move(transport);
    currentTransport_ = TransportType::Usb;
    registerRomfsTransport(transport_.get());

    if (!transport_->sendCommand(CART_INFO, &cartInfo_, &error)) {
        setError(error);
        disconnect();
        return false;
    }

    emit connectionStateChanged(true);
    return true;
}

bool RomfsDevice::connectRemote(const QHostAddress &address, quint16 port)
{
    disconnect();
    auto transport = std::make_unique<RemoteTransport>(address, port, this);
    QString error;
    if (!transport->connectDevice(&error)) {
        setError(error);
        return false;
    }

    transport_ = std::move(transport);
    currentTransport_ = TransportType::Remote;
    registerRomfsTransport(transport_.get());

    if (!transport_->sendCommand(CART_INFO, &cartInfo_, &error)) {
        setError(error);
        disconnect();
        return false;
    }

    emit connectionStateChanged(true);
    return true;
}

void RomfsDevice::disconnect()
{
    if (currentTransport_ == TransportType::None) {
        return;
    }

    QString error;
    if (!leaveSpiMode(&error)) {
        qWarning() << "Failed to switch flash back to quad mode:" << error;
    }
    if (transport_) {
        transport_->disconnectDevice();
    }
    resetConnectionState(true);
}

bool RomfsDevice::isConnected() const
{
    return currentTransport_ != TransportType::None;
}

RomfsDevice::TransportType RomfsDevice::transportType() const
{
    return currentTransport_;
}

QString RomfsDevice::lastError() const
{
    return lastError_;
}

QVector<RomfsEntry> RomfsDevice::list(const QString &path, QString *errorString)
{
    QVector<RomfsEntry> entries;

    bool ok = runRomfsOperation([&](QString *err) {
        entries = readDirectory(path, err);
        return err == nullptr || err->isEmpty();
    }, errorString);

    if (!ok && errorString && errorString->isEmpty()) {
        *errorString = lastError_;
    }
    return entries;
}
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
